icnagy/pe_microsynth/3dmodels/DP3T Slide Switch.step

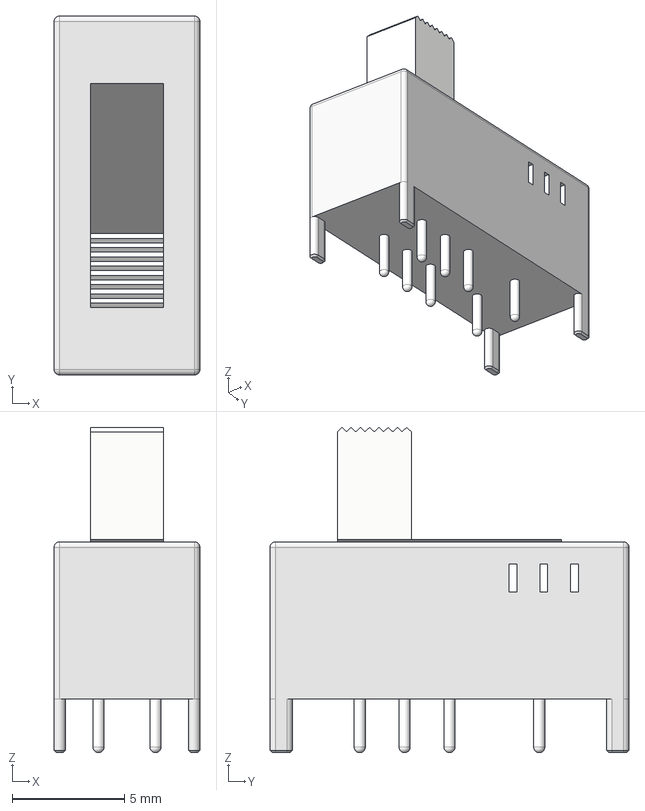
[picture p19: CAD file, 2020-04-17]
3dmodels/DP3T Slide Switch.step
6.50 x 16.0 x 14.5 mm
